bachmmmar/led_clock/src/leds.h

#pragma once

#include "NeoPixel/Adafruit_NeoPixel.h"
#include "config.h"
#include "logger.h"

class Time;

class Leds {

public:
    explicit Leds(LedConfig_t * config, Logger * logger);

    void setup(void);
    void update(const Time & current_time, const uint16_t & milliseconds_in_minute);
    void updateBrightness(const uint32_t & lux);

private:
    typedef struct {
        uint32_t hours;
        uint32_t minutes;
        uint32_t seconds;
        uint32_t marks;
    } colors_t;

    typedef union {
        uint32_t color;
        struct {
            uint8_t b;
            uint8_t g;
            uint8_t r;
            uint8_t dummy;
        } splitted;
    } color_t;

    typedef struct {
        int last_inner_pixel;
        int current_inner_pixel;
        int last_outer_pixel;
        int current_outer_pixel;
        color_t color;
    } effect_rotation_pxl_t;

    const colors_t BASE_COLOR;
    const colors_t MIN_COLOR;
    colors_t _dimmed_color;

    Logger * _logger;
    LedConfig_t * _config;
    uint8_t pxl_buffer[3*255];
    Adafruit_NeoPixel _inner_ring;
    Adafruit_NeoPixel _outer_ring;

    uint32_t _outer_ring_min_multiplier;
    uint32_t _outer_ring_second_multiplier;

    uint32_t _inner_ring_min_multiplier;
    uint32_t _inner_ring_second_multiplier;

    uint32_t _last_status_time_ms;

    #define NUM_ROTATION_PIXELS 7
    const effect_rotation_pxl_t BASE_ROTATION_PIXELS [NUM_ROTATION_PIXELS];
    const uint32_t MIN_ROTATION_PIXELS [NUM_ROTATION_PIXELS];
    const int16_t rotation_speed = 4;
    effect_rotation_pxl_t _dimmed_rotation_pixels [NUM_ROTATION_PIXELS];

    void showTime(const Time & current_time, uint16_t ms);
    void fullHourSpin(uint8_t rotations);
    static effect_rotation_pxl_t initRotationPxl(uint8_t pos, uint8_t max_pixel, uint8_t r, uint8_t g, uint8_t b);
    void updateInnerRotationPxl(effect_rotation_pxl_t * pxl);
    void updateOuterRotationPxl(effect_rotation_pxl_t *pxl);

    static void fixingClockRotation(uint8_t *hour, uint8_t *min, uint16_t *ms_in_min);
    void setInnerRingDefaults(void);
    void setOuterRingDefaults(void);
    void setTimeOnOuterRing(uint8_t hour, uint8_t min, uint16_t ms_in_min);
    void setTimeOnInnerRing(uint8_t hour, uint8_t min, uint16_t ms_in_min);

    static uint32_t scaleColor(const color_t & input, const color_t & min, uint16_t scale);
};
